LucaPavirani/iAcc/PSoC Code/Main.cydsn/Defines.h

/* ========================================
 *
 * Header file with useful defines
 *
 * ========================================
*/

#ifndef __DEFINES_H
    #define __DEFINES_H
    
    #include "cytypes.h"
    #include "stdio.h"
    
    #define INITIALIZATION  1
    #define READING         2
    #define VARIATION       3 //FS and So modifications
    #define TURNOFF         4
    #define CONNECTION      0

#endif
/* [] END OF FILE */
