LucaPavirani/iAcc/PSoC Code/Main.cydsn/ErrorCodes.h

/**
*   \brief Error codes.
* 
*   This definition defines several error codes that will
*   be used throughout the project.
*/
#ifndef __ERRORCODES_H
    #define __ERRORCODES_H
    
    typedef enum {
        NO_ERROR,           ///< No error generated
        ERROR               ///< Error generated
    } ErrorCode;

#endif
/* [] END OF FILE */
