LucaPavirani/iAcc/PSoC Code/Main.cydsn/codegentemp/Pin_LED_info_aliases.h

/*******************************************************************************
* File Name: Pin_LED_info.h  
* Version 2.20
*
* Description:
*  This file contains the Alias definitions for Per-Pin APIs in cypins.h. 
*  Information on using these APIs can be found in the System Reference Guide.
*
* Note:
*
********************************************************************************
* Copyright 2008-2015, Cypress Semiconductor Corporation.  All rights reserved.
* You may use this file only in accordance with the license, terms, conditions, 
* disclaimers, and limitations in the end user license agreement accompanying 
* the software package with which this file was provided.
*******************************************************************************/

#if !defined(CY_PINS_Pin_LED_info_ALIASES_H) /* Pins Pin_LED_info_ALIASES_H */
#define CY_PINS_Pin_LED_info_ALIASES_H

#include "cytypes.h"
#include "cyfitter.h"


/***************************************
*              Constants        
***************************************/
#define Pin_LED_info_0			(Pin_LED_info__0__PC)
#define Pin_LED_info_0_INTR	((uint16)((uint16)0x0001u << Pin_LED_info__0__SHIFT))

#define Pin_LED_info_INTR_ALL	 ((uint16)(Pin_LED_info_0_INTR))

#endif /* End Pins Pin_LED_info_ALIASES_H */


/* [] END OF FILE */
