LucaPavirani/iAcc/PSoC Code/Main.cydsn/codegentemp/isr.h

/*******************************************************************************
* File Name: isr.h
* Version 1.71
*
*  Description:
*   Provides the function definitions for the Interrupt Controller.
*
*
********************************************************************************
* Copyright 2008-2015, Cypress Semiconductor Corporation.  All rights reserved.
* You may use this file only in accordance with the license, terms, conditions, 
* disclaimers, and limitations in the end user license agreement accompanying 
* the software package with which this file was provided.
*******************************************************************************/
#if !defined(CY_ISR_isr_H)
#define CY_ISR_isr_H


#include <cytypes.h>
#include <cyfitter.h>

/* Interrupt Controller API. */
void isr_Start(void);
void isr_StartEx(cyisraddress address);
void isr_Stop(void);

CY_ISR_PROTO(isr_Interrupt);

void isr_SetVector(cyisraddress address);
cyisraddress isr_GetVector(void);

void isr_SetPriority(uint8 priority);
uint8 isr_GetPriority(void);

void isr_Enable(void);
uint8 isr_GetState(void);
void isr_Disable(void);

void isr_SetPending(void);
void isr_ClearPending(void);


/* Interrupt Controller Constants */

/* Address of the INTC.VECT[x] register that contains the Address of the isr ISR. */
#define isr_INTC_VECTOR            ((reg32 *) isr__INTC_VECT)

/* Address of the isr ISR priority. */
#define isr_INTC_PRIOR             ((reg8 *) isr__INTC_PRIOR_REG)

/* Priority of the isr interrupt. */
#define isr_INTC_PRIOR_NUMBER      isr__INTC_PRIOR_NUM

/* Address of the INTC.SET_EN[x] byte to bit enable isr interrupt. */
#define isr_INTC_SET_EN            ((reg32 *) isr__INTC_SET_EN_REG)

/* Address of the INTC.CLR_EN[x] register to bit clear the isr interrupt. */
#define isr_INTC_CLR_EN            ((reg32 *) isr__INTC_CLR_EN_REG)

/* Address of the INTC.SET_PD[x] register to set the isr interrupt state to pending. */
#define isr_INTC_SET_PD            ((reg32 *) isr__INTC_SET_PD_REG)

/* Address of the INTC.CLR_PD[x] register to clear the isr interrupt. */
#define isr_INTC_CLR_PD            ((reg32 *) isr__INTC_CLR_PD_REG)


#endif /* CY_ISR_isr_H */


/* [] END OF FILE */
