LucaPavirani/iAcc/PSoC Code/Main.cydsn/codegentemp/isr_RX.h

/*******************************************************************************
* File Name: isr_RX.h
* Version 1.71
*
*  Description:
*   Provides the function definitions for the Interrupt Controller.
*
*
********************************************************************************
* Copyright 2008-2015, Cypress Semiconductor Corporation.  All rights reserved.
* You may use this file only in accordance with the license, terms, conditions, 
* disclaimers, and limitations in the end user license agreement accompanying 
* the software package with which this file was provided.
*******************************************************************************/
#if !defined(CY_ISR_isr_RX_H)
#define CY_ISR_isr_RX_H


#include <cytypes.h>
#include <cyfitter.h>

/* Interrupt Controller API. */
void isr_RX_Start(void);
void isr_RX_StartEx(cyisraddress address);
void isr_RX_Stop(void);

CY_ISR_PROTO(isr_RX_Interrupt);

void isr_RX_SetVector(cyisraddress address);
cyisraddress isr_RX_GetVector(void);

void isr_RX_SetPriority(uint8 priority);
uint8 isr_RX_GetPriority(void);

void isr_RX_Enable(void);
uint8 isr_RX_GetState(void);
void isr_RX_Disable(void);

void isr_RX_SetPending(void);
void isr_RX_ClearPending(void);


/* Interrupt Controller Constants */

/* Address of the INTC.VECT[x] register that contains the Address of the isr_RX ISR. */
#define isr_RX_INTC_VECTOR            ((reg32 *) isr_RX__INTC_VECT)

/* Address of the isr_RX ISR priority. */
#define isr_RX_INTC_PRIOR             ((reg8 *) isr_RX__INTC_PRIOR_REG)

/* Priority of the isr_RX interrupt. */
#define isr_RX_INTC_PRIOR_NUMBER      isr_RX__INTC_PRIOR_NUM

/* Address of the INTC.SET_EN[x] byte to bit enable isr_RX interrupt. */
#define isr_RX_INTC_SET_EN            ((reg32 *) isr_RX__INTC_SET_EN_REG)

/* Address of the INTC.CLR_EN[x] register to bit clear the isr_RX interrupt. */
#define isr_RX_INTC_CLR_EN            ((reg32 *) isr_RX__INTC_CLR_EN_REG)

/* Address of the INTC.SET_PD[x] register to set the isr_RX interrupt state to pending. */
#define isr_RX_INTC_SET_PD            ((reg32 *) isr_RX__INTC_SET_PD_REG)

/* Address of the INTC.CLR_PD[x] register to clear the isr_RX interrupt. */
#define isr_RX_INTC_CLR_PD            ((reg32 *) isr_RX__INTC_CLR_PD_REG)


#endif /* CY_ISR_isr_RX_H */


/* [] END OF FILE */
